joranderaaff/portalturret/electronics/v3/docs/pcb_1.jpg

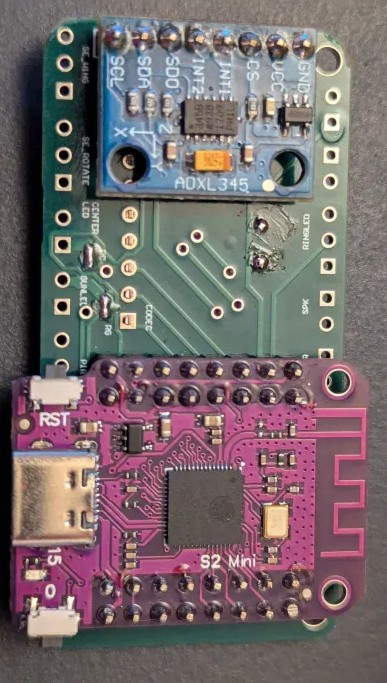
electronics/v3/docs/pcb_1.jpg
