joranderaaff/portalturret/src/ESP32Servo.h

#include <Arduino.h>

#define DUTYCYLEMIN 411
#define DUTYCYLEMAX 820

class Servo {
public:
  void attach(int pin, int channel, int freq, int resolution) {
    this->channel = channel;
    ledcSetup(channel, freq, resolution);
    pinMode(pin, OUTPUT);
    ledcAttachPin(pin, channel);
  }
  void write(int value) {
    int servoValue = value * (DUTYCYLEMAX - DUTYCYLEMIN) / 180 + DUTYCYLEMIN;
    ledcWrite(channel, servoValue);
  }
private:
  int channel;
};
